schnorea/IoT-Remote-Robot/assets/IMG_5102.PNG

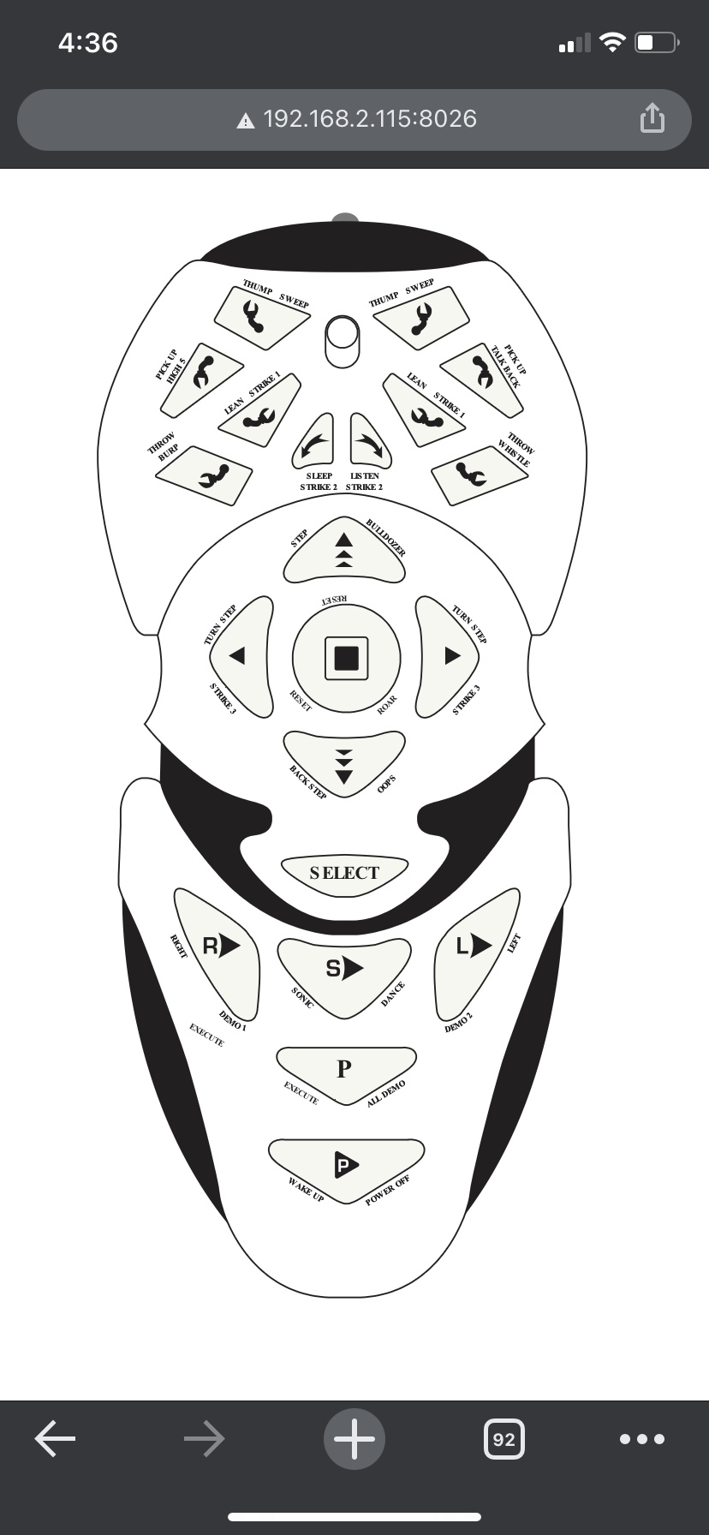
assets/IMG_5102.PNG
